makingdevices/OpenReflowPlate/Kicad/OpenReflowPlate/pictures/pic0.png

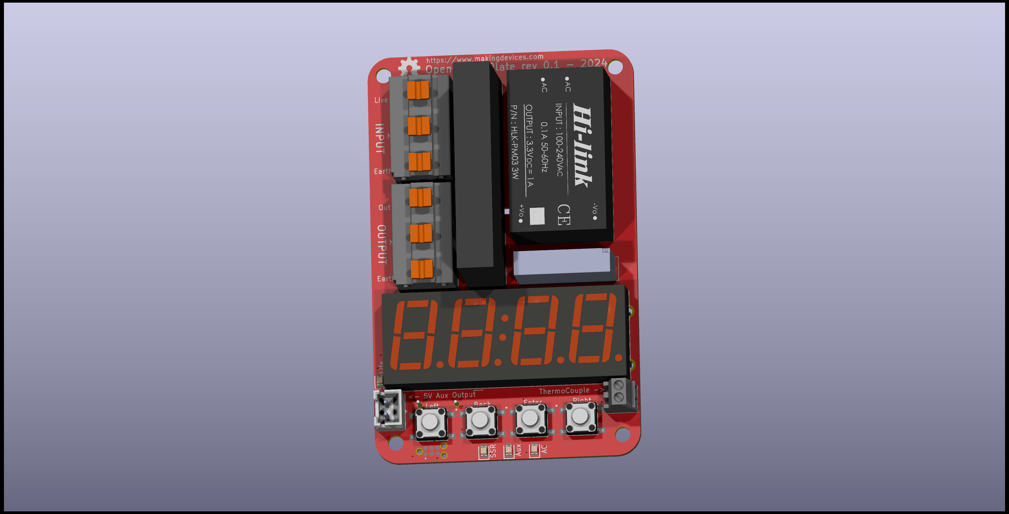
Kicad/OpenReflowPlate/pictures/pic0.png
