makingdevices/OpenReflowPlate/Kicad/OpenReflowPlate/pictures/pic26.png

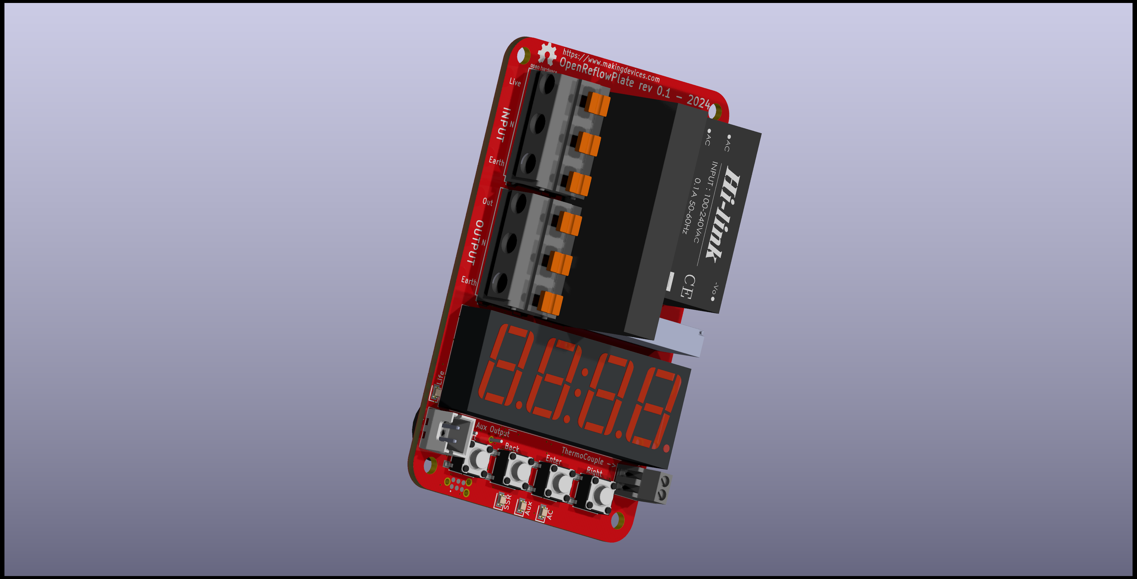
Kicad/OpenReflowPlate/pictures/pic26.png
