makingdevices/OpenReflowPlate/Kicad/OpenReflowPlate/pictures/pic38.png

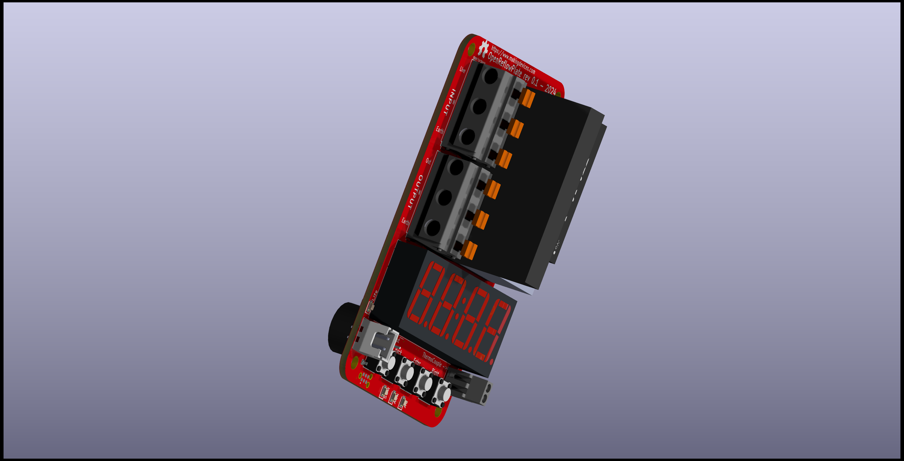
Kicad/OpenReflowPlate/pictures/pic38.png
