makingdevices/OpenReflowPlate/Kicad/OpenReflowPlate/pictures/pic45.png

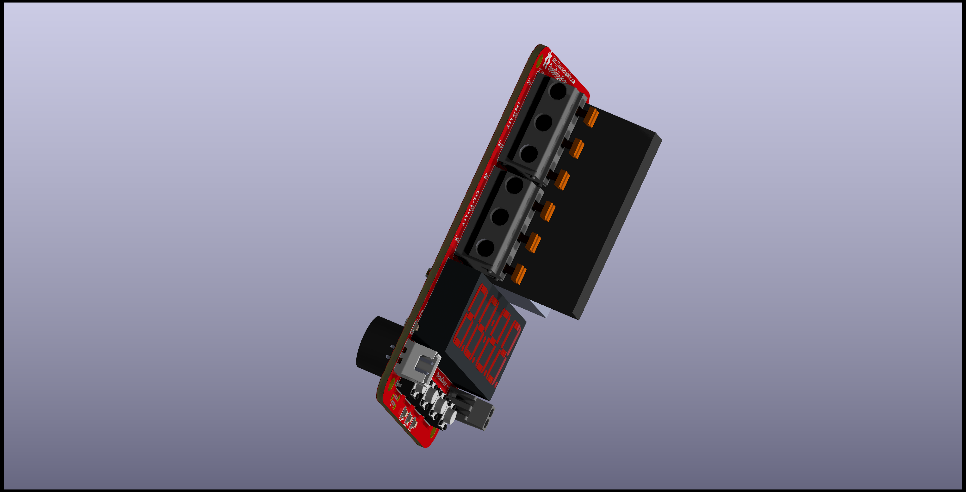
Kicad/OpenReflowPlate/pictures/pic45.png
