makingdevices/OpenReflowPlate/Kicad/OpenReflowPlate/pictures/pic52.png

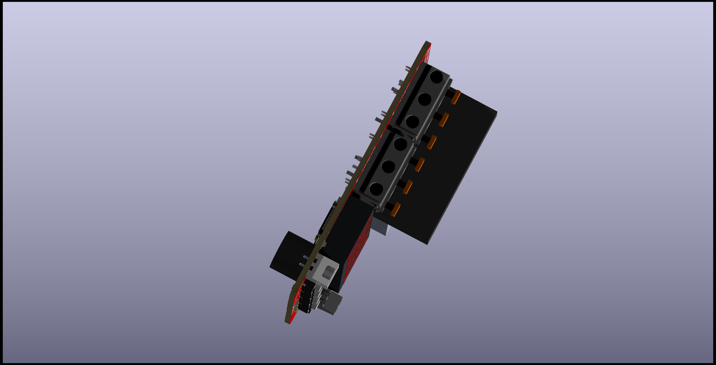
Kicad/OpenReflowPlate/pictures/pic52.png
