makingdevices/OpenReflowPlate/Kicad/OpenReflowPlate/pictures/pic77.png

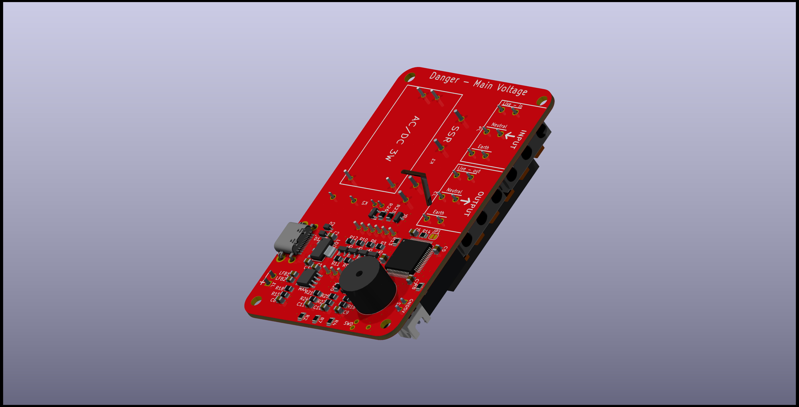
Kicad/OpenReflowPlate/pictures/pic77.png
