makingdevices/OpenReflowPlate/Kicad/OpenReflowPlate/pictures/pic87.png

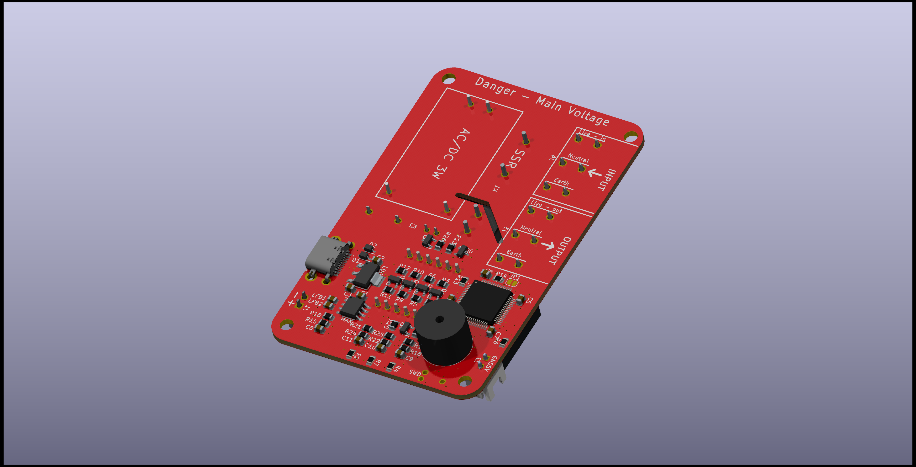
Kicad/OpenReflowPlate/pictures/pic87.png
