makingdevices/OpenReflowPlate/Kicad/OpenReflowPlate/pictures/pic130.png

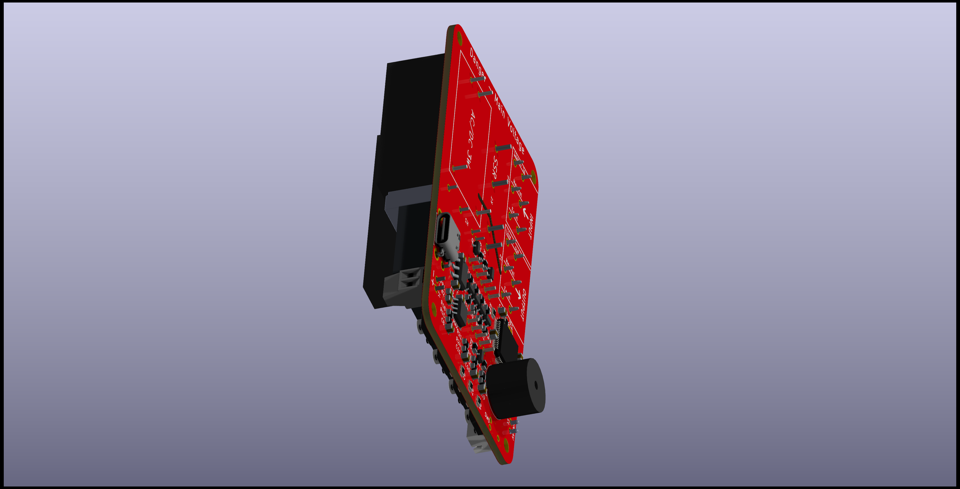
Kicad/OpenReflowPlate/pictures/pic130.png
