makingdevices/OpenReflowPlate/Kicad/OpenReflowPlate/pictures/pic136.png

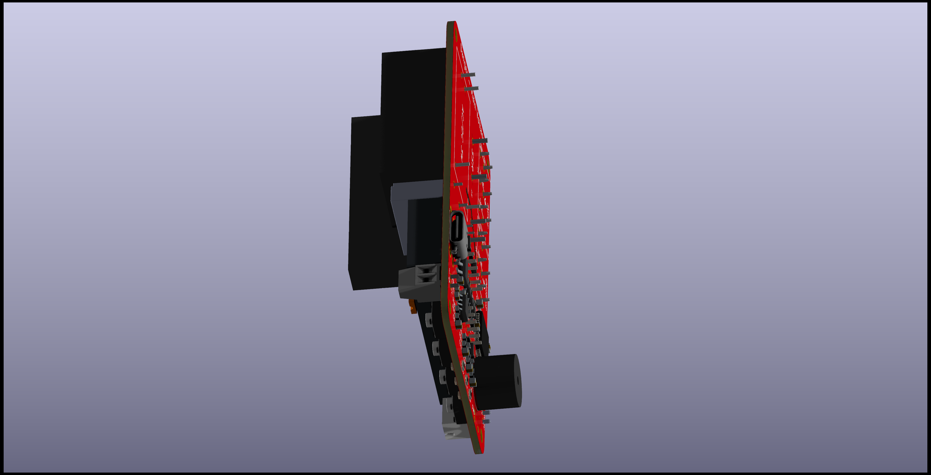
Kicad/OpenReflowPlate/pictures/pic136.png
