makingdevices/OpenReflowPlate/Kicad/OpenReflowPlate/pictures/pic149.png

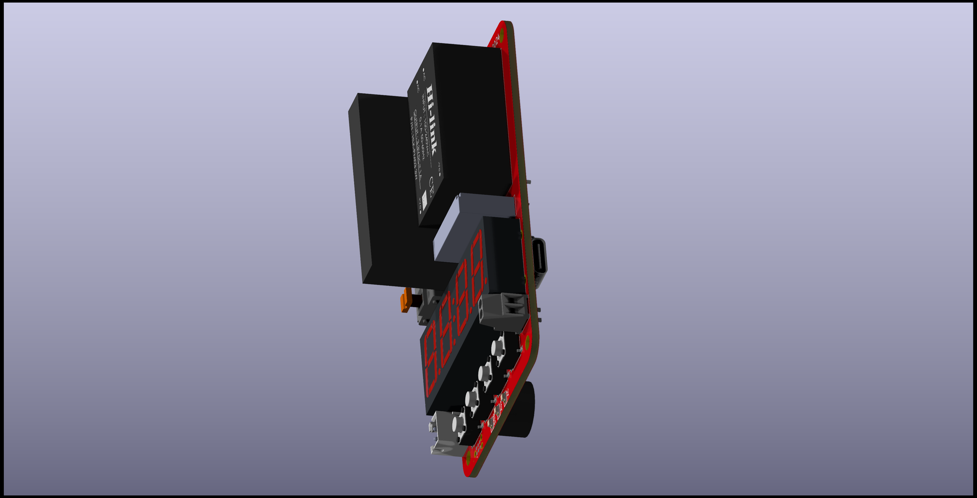
Kicad/OpenReflowPlate/pictures/pic149.png
