makingdevices/OpenReflowPlate/Kicad/OpenReflowPlate/pictures_without/pic29.png

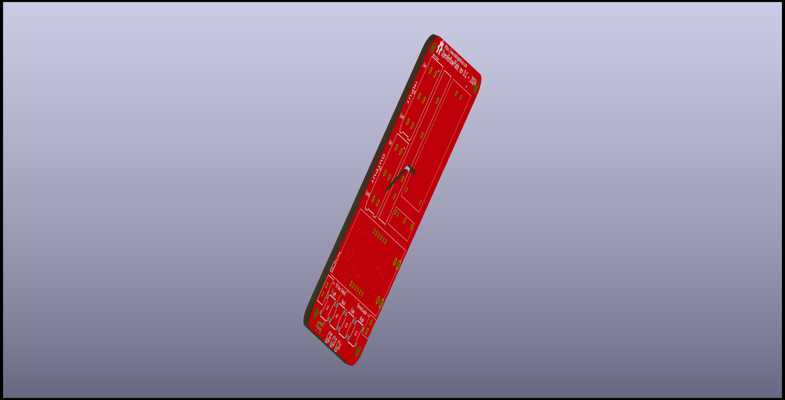
Kicad/OpenReflowPlate/pictures_without/pic29.png
