makingdevices/OpenReflowPlate/Kicad/OpenReflowPlate/pictures_without/pic35.png

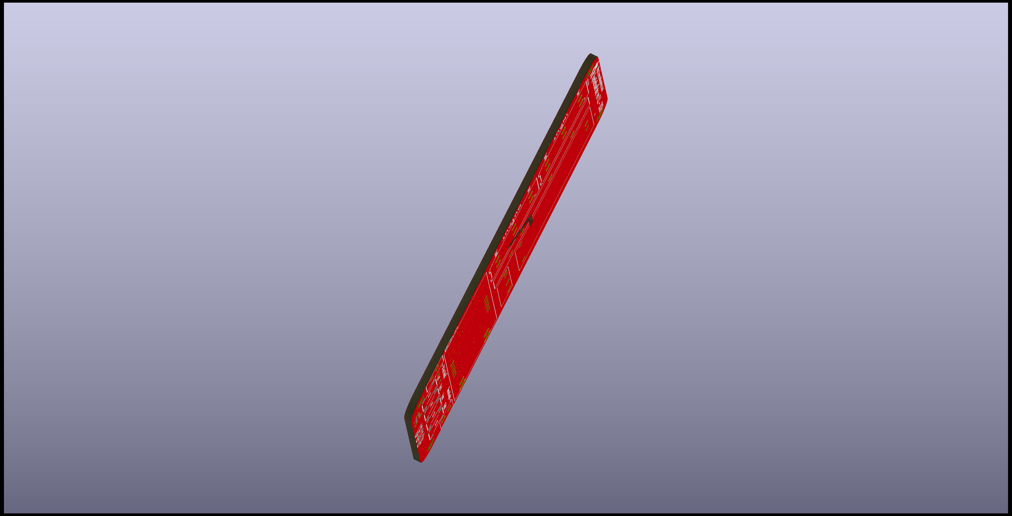
Kicad/OpenReflowPlate/pictures_without/pic35.png
