makingdevices/OpenReflowPlate/Kicad/OpenReflowPlate/pictures_without/pic41.png

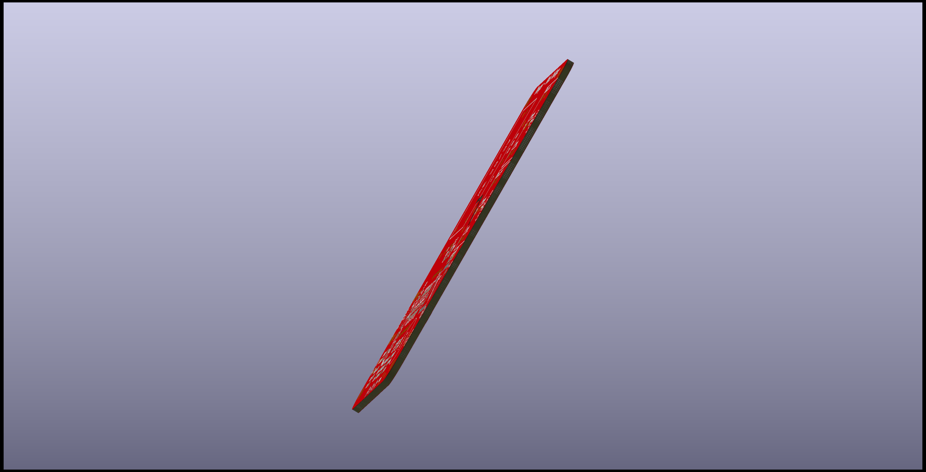
Kicad/OpenReflowPlate/pictures_without/pic41.png
