makingdevices/OpenReflowPlate/Kicad/OpenReflowPlate/pictures_without/pic52.png

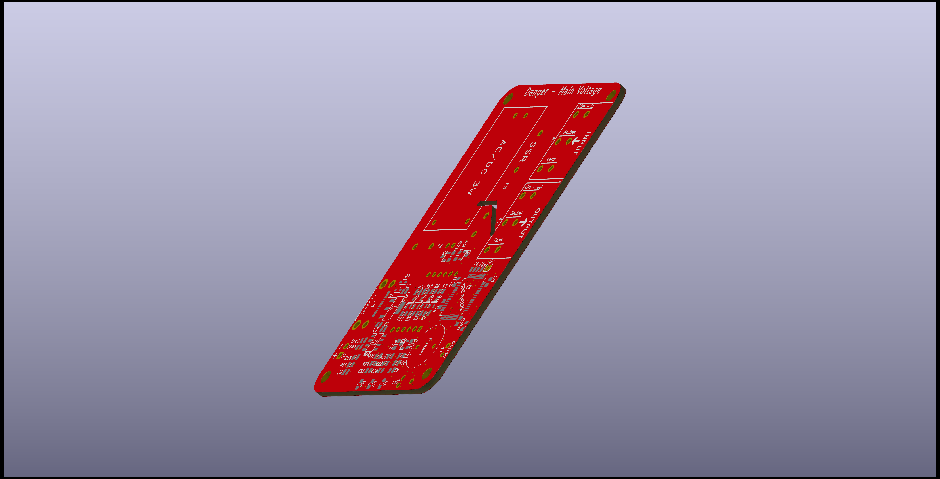
Kicad/OpenReflowPlate/pictures_without/pic52.png
