makingdevices/OpenReflowPlate/Kicad/OpenReflowPlate/pictures/OpenReflowPlate_test1.png

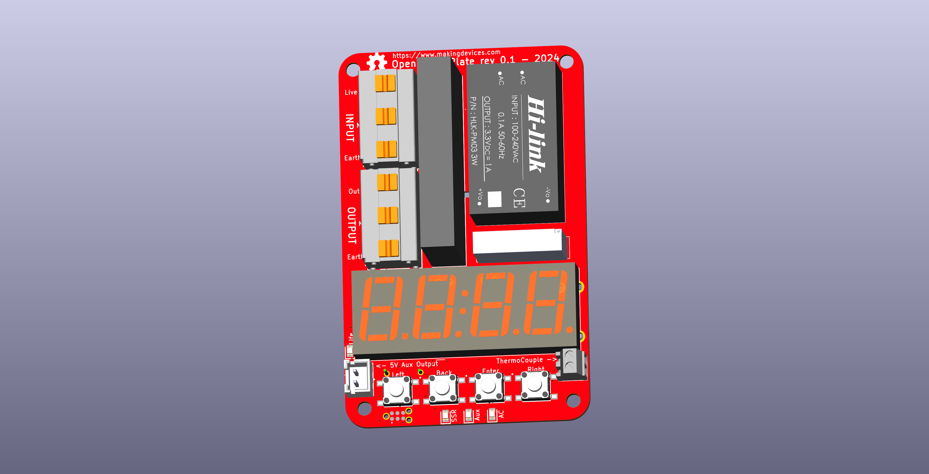
Kicad/OpenReflowPlate/pictures/OpenReflowPlate_test1.png
